UzixLS/zx-multisound/cpld/tb/circuit.asc

C1: cap; 10n
C2: cap; 1n
R1: res; 100k
R6: res; 1k
V5: voltage; PWL file=testbench_pwl.txt
Named nets: 0, Out, In, Mid
.tran 10m
